smartboxchannel/eON-AQSENS_213_V2_ED3-EFEKTALAB/IMAGES/IMG_20210524_220622.jpg

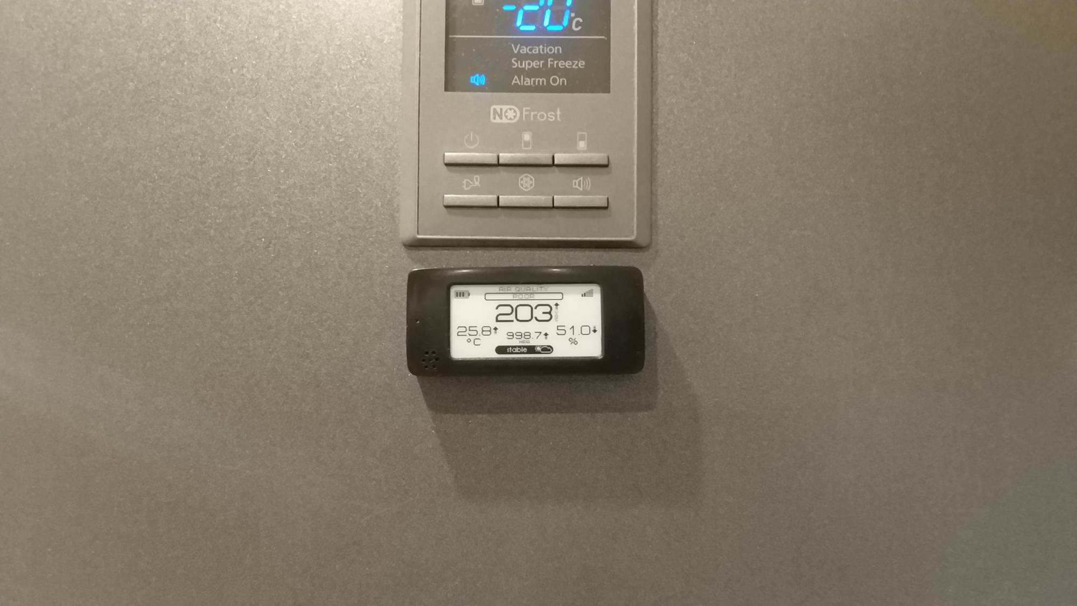
IMAGES/IMG_20210524_220622.jpg
