smartboxchannel/eON-AQSENS_213_V2_ED3-EFEKTALAB/CODE/ARDUINO/imagedata.cpp

// ###################   Mini air quality and wither station with electronic ink display 2.13 Inch | nRF52   ############### //
//                                                                                                                           //
//        @filename   :   MWS213_V2R3_ED3.ino                                                                                //
//        @brief en   :   Wireless, battery-operated air quality(VOC Sensor SGP40), temperature,humidity and pressure        //
//                        sensor(BME280) with electronic ink display(Good Display GDEH0213B72, GDEH0213B73, Waveshare V2).   //
//                        Works on SOC nRF52.                                                                                //
//        @brief ru   :   Беcпроводной, батарейный датчик качества воздуха (ЛОС сенсорс SGP40), температуры, влажности       //
//                        и давления(BME280) с дисплеем на электронных чернилах(Good Display GDEH0213B72, GDEH0213B73,       //
//                        Waveshare V2).                                                                                     //
//                        Работает на nRF52832, nRF52840.                                                                    //
//                                                                                                                           //
//        @author     :   Andrew Lamchenko aka Berk                                                                          //
//                                                                                                                           //
//        Copyright (C) 2021, EFEKTALAB                                                                                      //
//        Copyright (c) 2020, Sensirion AG                                                                                   //
//        Copyright (c) 2020, Bosch Sensortec GmbH. All rights reserved.                                                     //
//        Copyright (c) 2014-2015, Arduino LLC.  All right reserved.                                                         //
//        Copyright (c) 2016, Arduino Srl.  All right reserved.                                                              //
//        Copyright (c) 2017, Sensnology AB. All right reserved.                                                             //
//        Copyright (C) 2020, Waveshare                                                                                      //
//                                                                                                                           //
// ######################################################################################################################### //

#include "imagedata.h"
#include <avr/pgmspace.h>


const unsigned char Especially[] PROGMEM = { /* 0X01,0X01,0XB4,0X00,0X69,0X00, */
0X00,0X00,0X00,0X00,0X00,0X00,0X00,0X00,0X00,0X00,0X00,0X00,0X00,0X00,0X00,0X00,
0X00,0X00,0X00,0X00,0X00,0X00,0X00,0X00,0X00,0X00,0X00,0X00,0X00,0X00,0X00,0X00,
0X00,0X00,0X00,0X00,0X00,0X01,0XFC,0X00,0X00,0X00,0X00,0X00,0X00,0X00,0X00,0X00,
0X00,0X00,0X00,0X01,0X04,0X00,0X00,0X00,0X00,0X00,0X3F,0XFF,0XC0,0X00,0X00,0X00,
0X00,0X01,0X04,0X00,0X00,0X00,0X00,0X00,0X3F,0XFF,0XC0,0X00,0X00,0X00,0X00,0X01,
0X04,0X00,0X00,0X00,0X00,0X00,0X30,0X60,0XC0,0X00,0X00,0X00,0X00,0X01,0X04,0X00,
0X00,0X00,0X00,0X00,0X30,0X60,0XC0,0X00,0X00,0X00,0X00,0X01,0X04,0X07,0XF0,0X00,
0X00,0X00,0X30,0X60,0XC0,0X00,0X00,0X00,0X00,0X00,0XF8,0X04,0X40,0X00,0X00,0X00,
0X30,0X60,0XC0,0X00,0X00,0X00,0X00,0X00,0X00,0X04,0X40,0X00,0X00,0X00,0X30,0X60,
0XC0,0X00,0X00,0X00,0X00,0X00,0X00,0X04,0X40,0X00,0X00,0X00,0X30,0X60,0XC0,0X00,
0X00,0X00,0X00,0X00,0XF8,0X04,0X40,0X00,0X00,0X00,0X30,0X60,0XC0,0X00,0X00,0X00,
0X00,0X01,0X04,0X04,0X40,0X00,0X00,0X00,0X30,0X60,0XC0,0X00,0X00,0X00,0X00,0X01,
0X04,0X03,0X80,0X00,0X00,0X00,0X30,0X60,0XC0,0X00,0X00,0X00,0X00,0X01,0X04,0X00,
0X00,0X00,0X00,0X00,0X30,0X60,0XC0,0X00,0X00,0X00,0X00,0X01,0X04,0X00,0X00,0X00,
0X00,0X00,0X30,0X60,0XC0,0X00,0X00,0X00,0X00,0X01,0X04,0X00,0X00,0X00,0X00,0X00,
0X30,0X60,0XC0,0X00,0X00,0X00,0X00,0X00,0XF8,0X03,0XF0,0X00,0X00,0X00,0X30,0X00,
0XC0,0X00,0X00,0X00,0X00,0X00,0X00,0X04,0X40,0X00,0X00,0X00,0X30,0X00,0XC0,0X00,
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
0X00,0X00,0X00,0X00,0X00,0X07,0XFC,0X00,0X00,0X00,0X00,0X00,0X00,0X00,0X00,0X00,
0X00,0X00,0X00,0X00,0X00,0X00,0X00,0X00,0X00,0X00,0X00,0X00,0X00,0X00,0X00,0X00,
0X00,0X00,0X00,0X00,0X00,0X00,0X00,0X00,0X00,0X00,0X00,0X00,0X00,0X00,0X00,0X00,
0X00,0X00,0X00,0X00,0X00,0X00,0X00,0X00,};
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
